ernesto-g/PolySynth/PCB/7th_VOICE_PCB/PCB_TO_PRINT.png

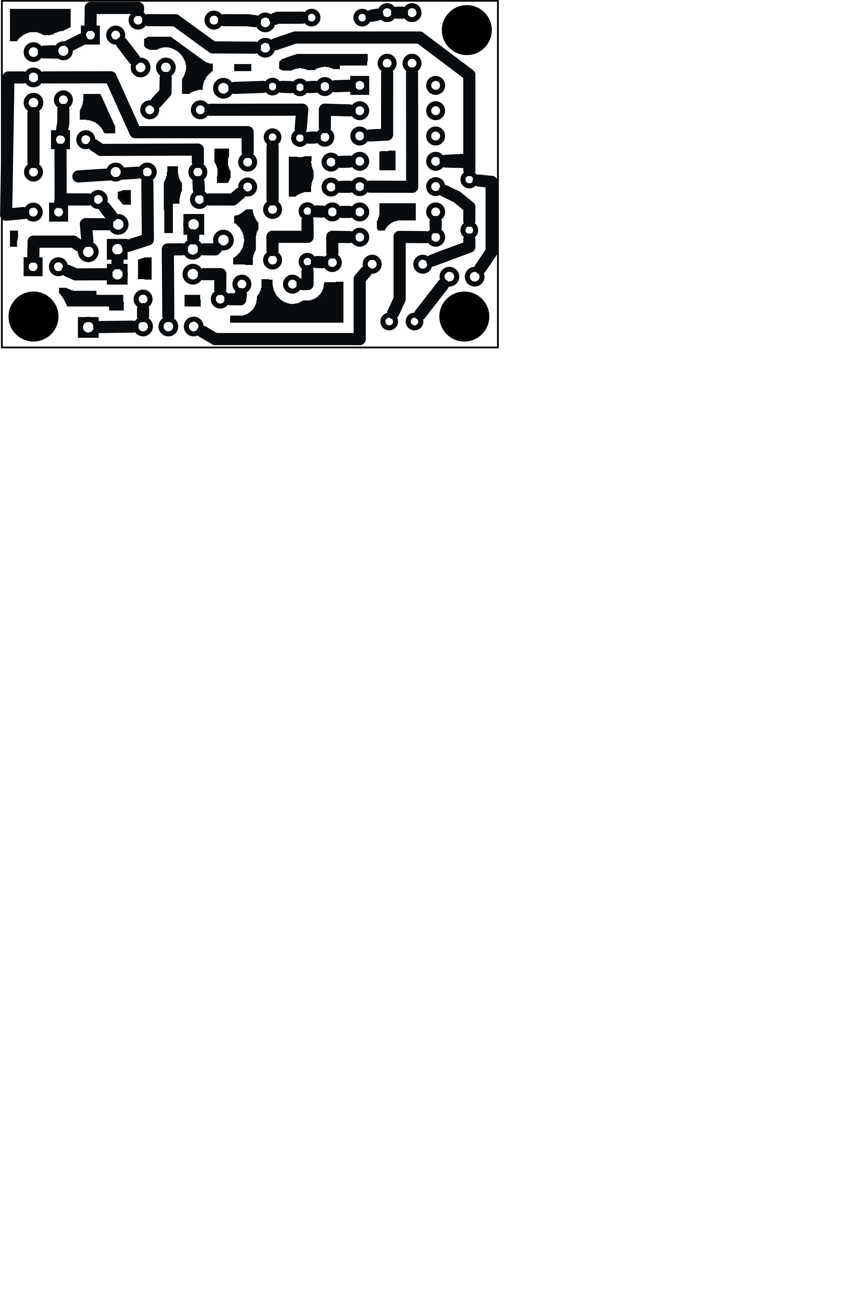
PCB/7th_VOICE_PCB/PCB_TO_PRINT.png
