ernesto-g/PolySynth/PCB/VCF_PCB/VCF_PCB_TO_PRINT.png

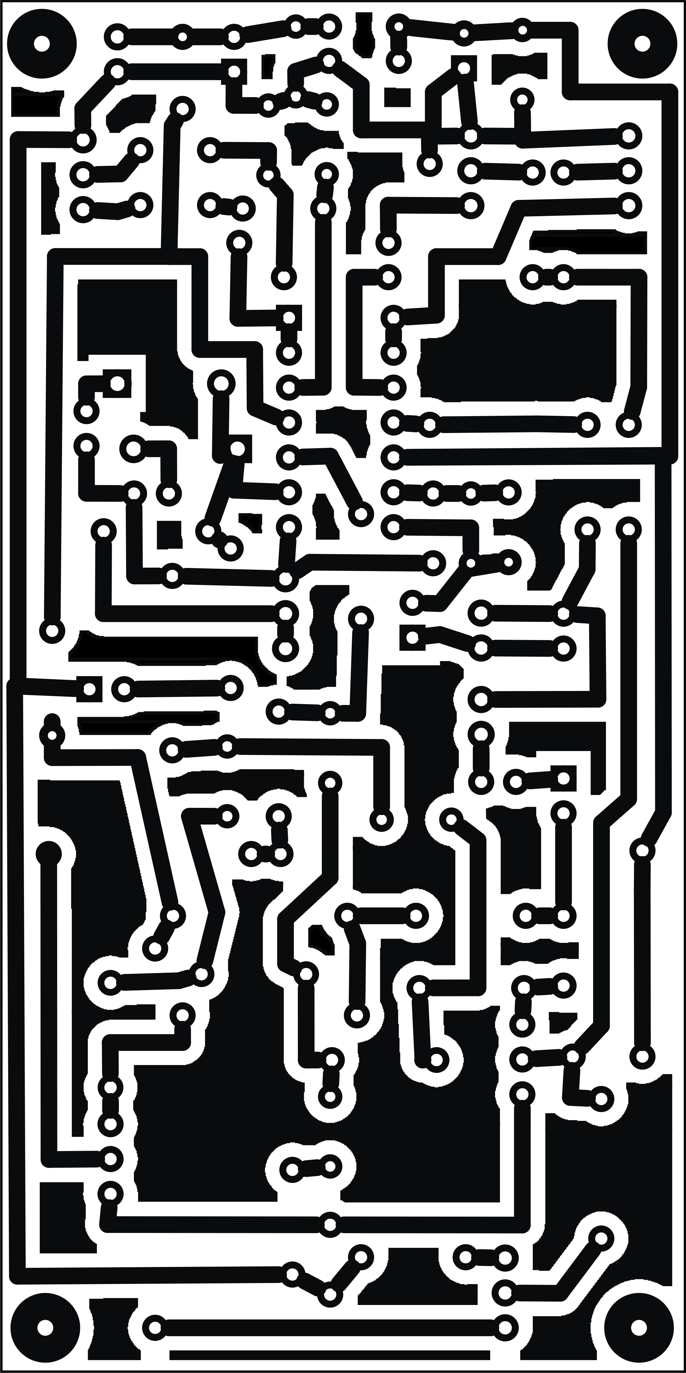
PCB/VCF_PCB/VCF_PCB_TO_PRINT.png
