ernesto-g/PolySynth/PCB/VOICES_PCB/VOICES_PCB_TO_PRINT.png

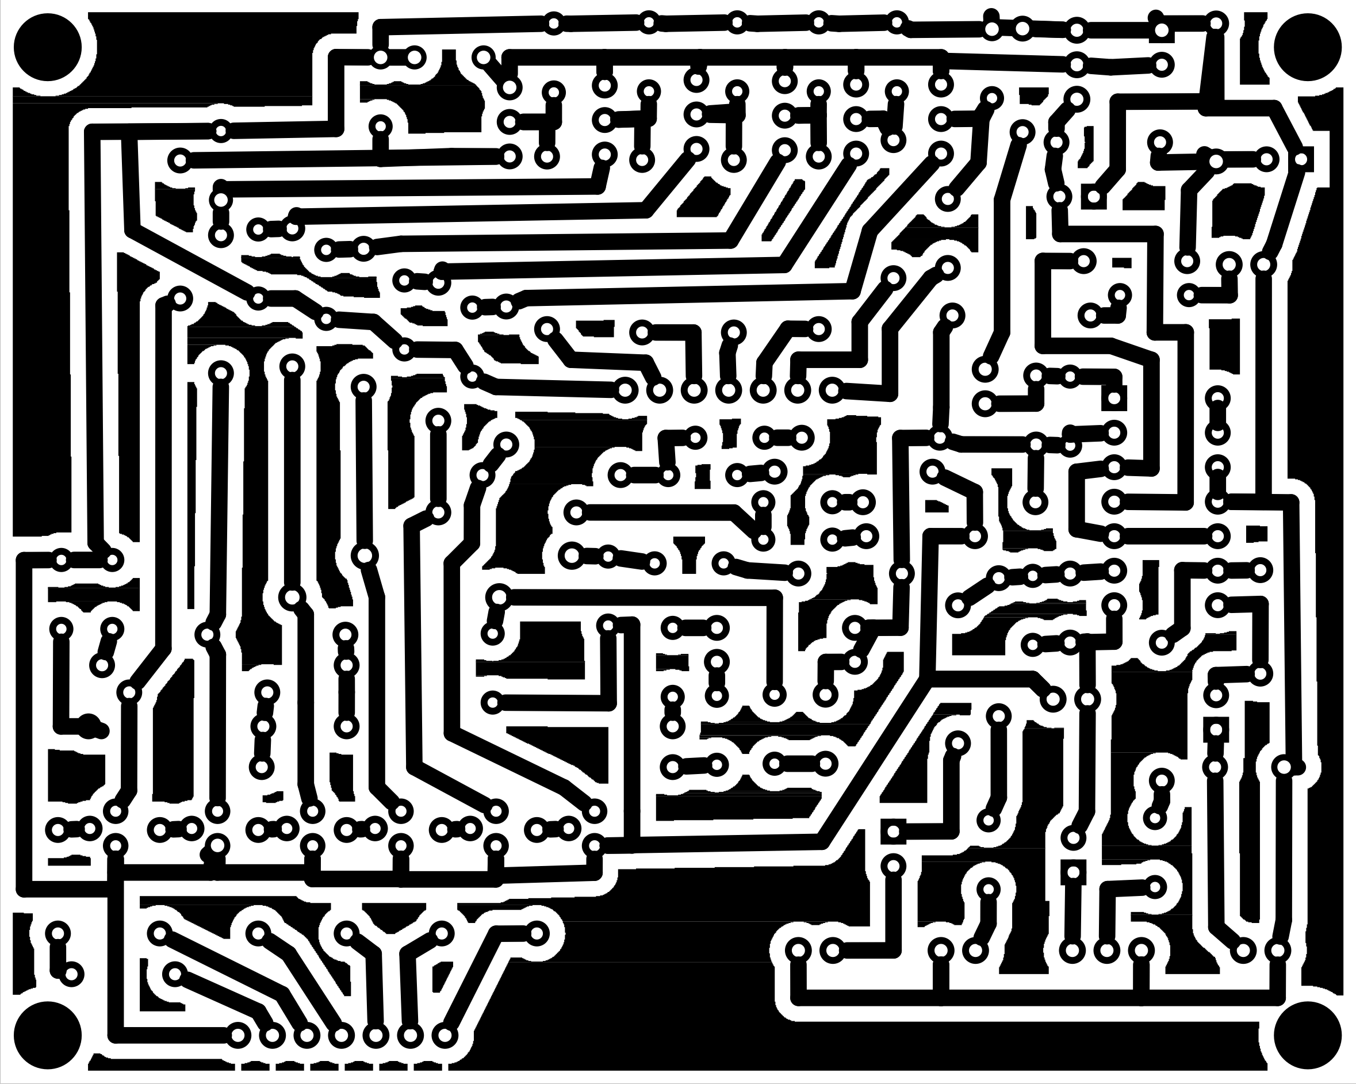
PCB/VOICES_PCB/VOICES_PCB_TO_PRINT.png
