ernesto-g/PolySynth/PCB/DIGITAL_PCB/DIGITAL_etch_silk_bottom.pdf

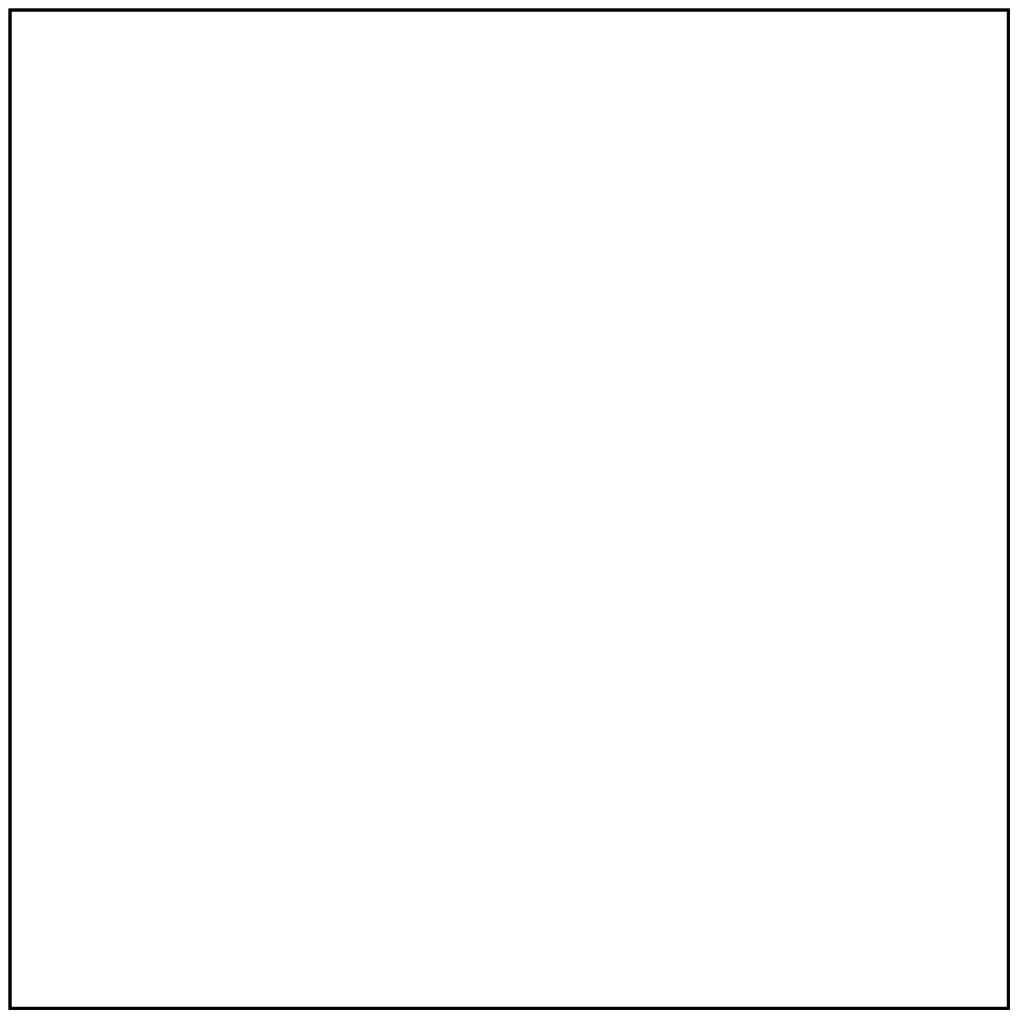
[picture p20: page 1]
