ernesto-g/PolySynth/PCB/DIGITAL_PCB/DIGITAL_etch_silk_top.pdf

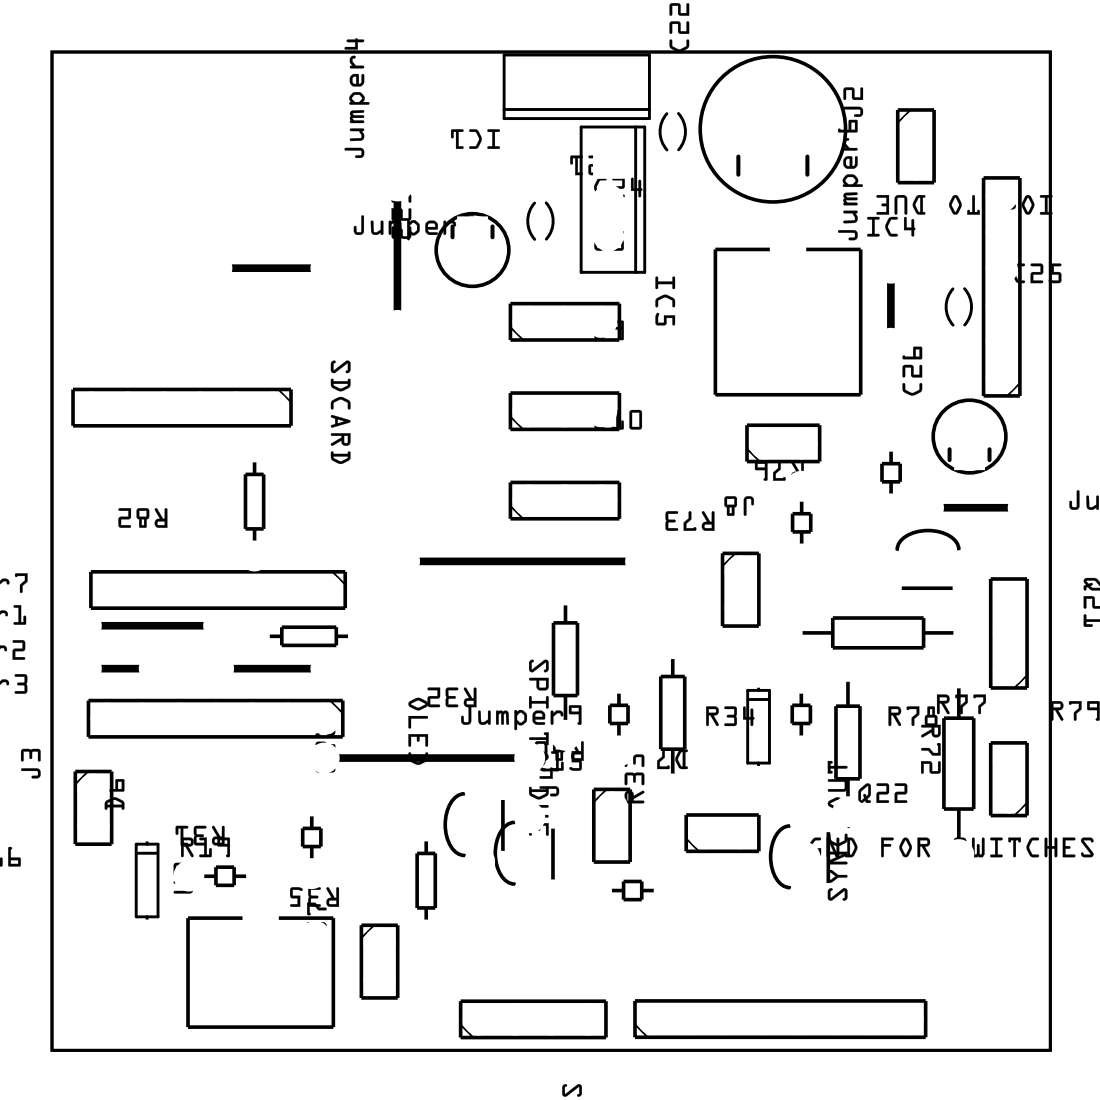
[picture p21: page 1]
