ernesto-g/PolySynth/PCB/DIGITAL_PCB/DIGITAL_etch_silk_top_mirror.pdf

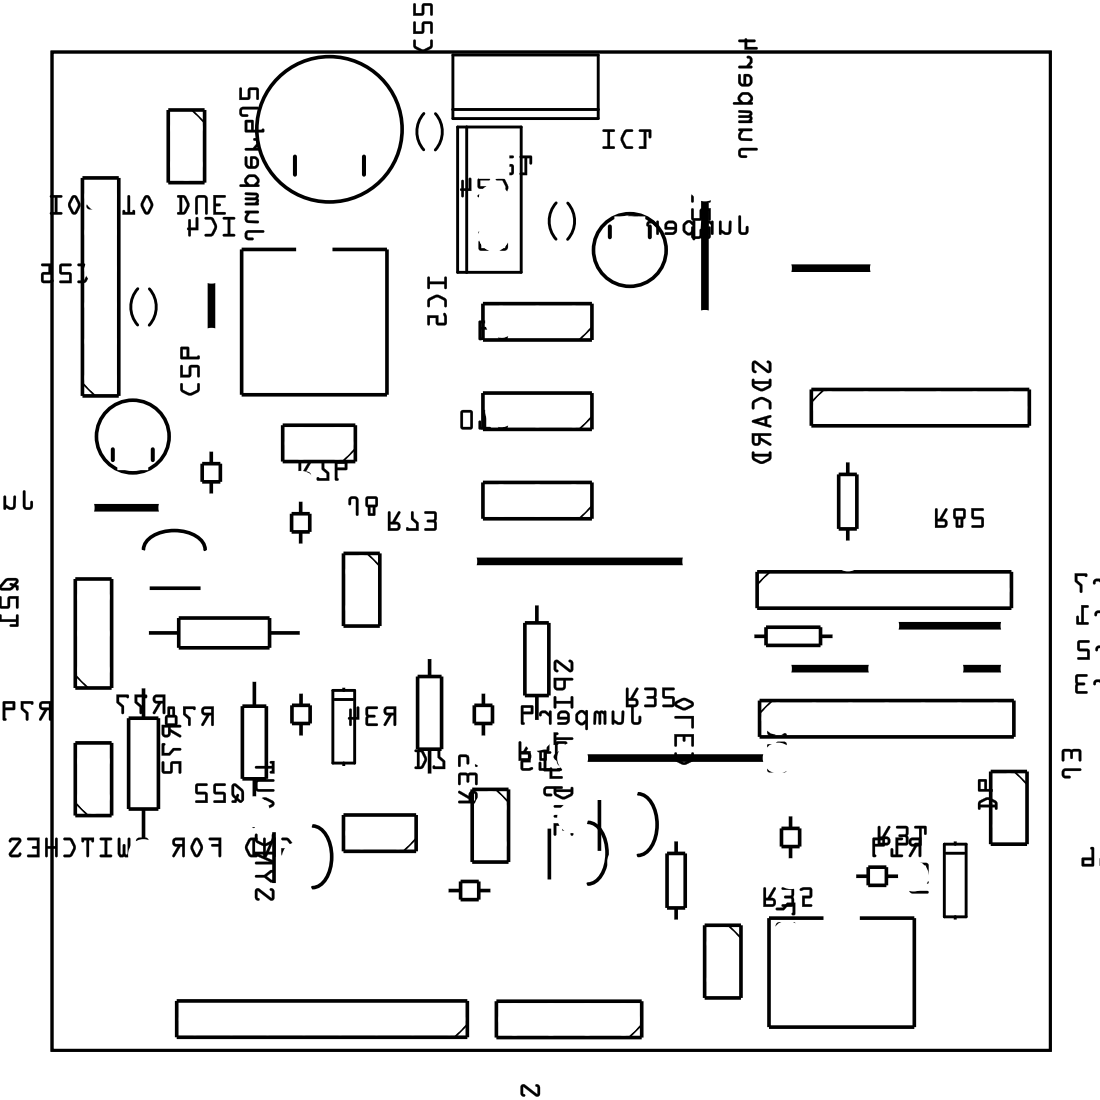
[picture p22: page 1]
