ernesto-g/PolySynth/PCB/VOICES_PCB/VOICES_etch_copper_bottom.pdf

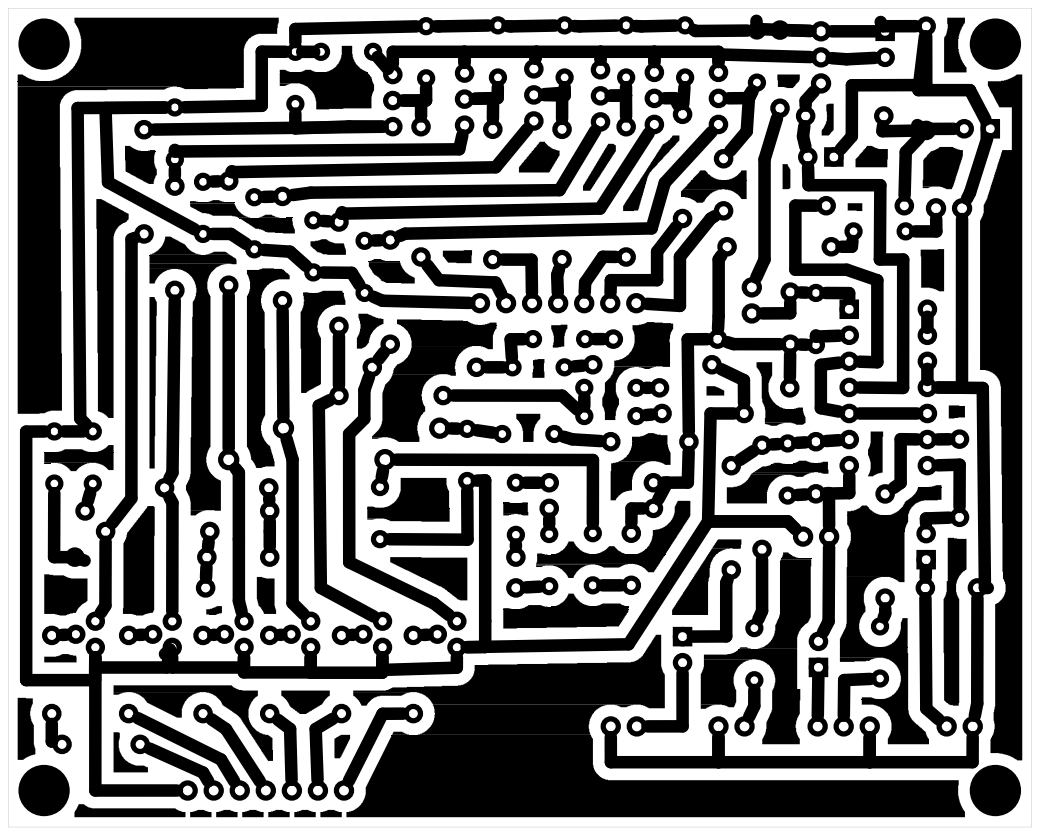
[picture p23: page 1]
