ernesto-g/PolySynth/PCB/VOICES_PCB/VOICES_etch_copper_bottom_mirror.pdf

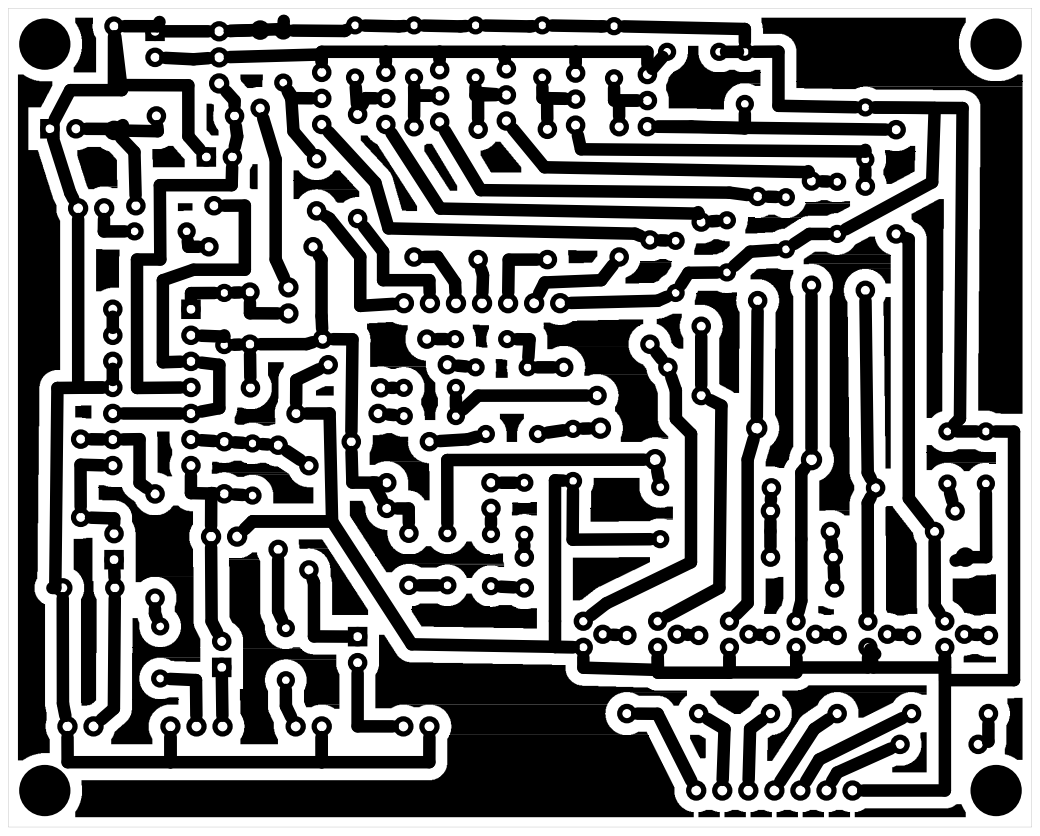
[picture p24: page 1]
