ernesto-g/PolySynth/PCB/VOICES_PCB/VOICES_etch_copper_top.pdf

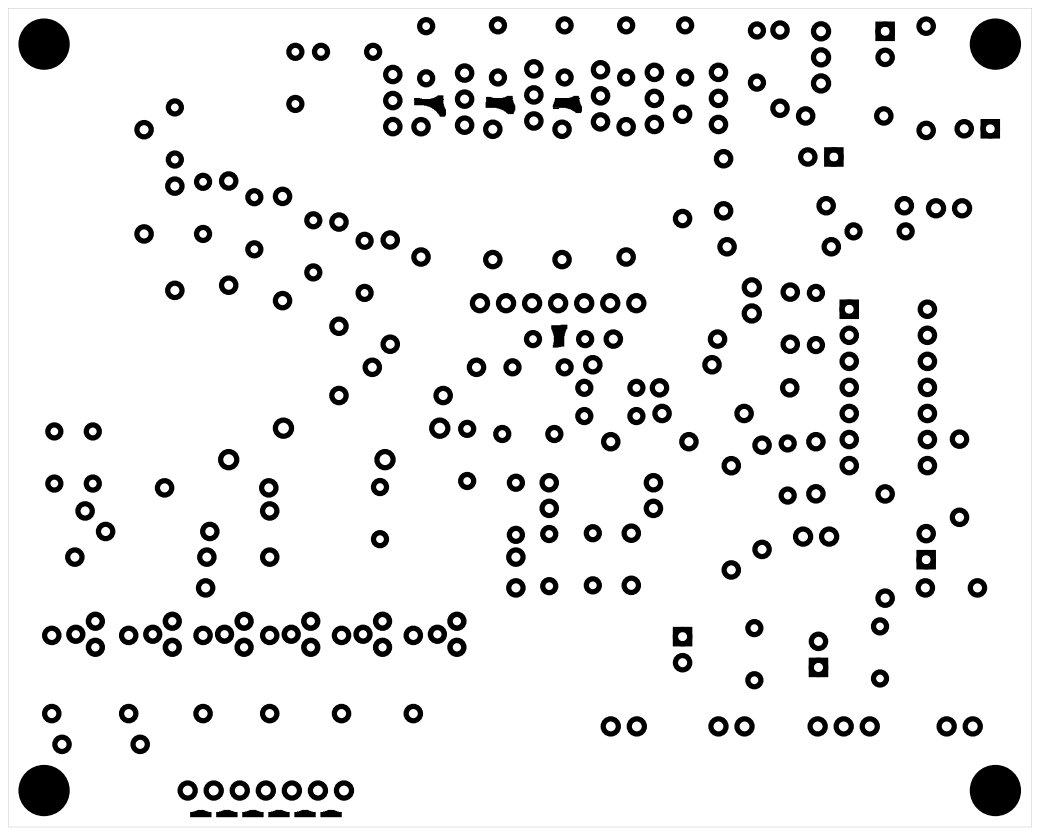
[picture p25: page 1]
