ernesto-g/PolySynth/PCB/VOICES_PCB/VOICES_etch_copper_top_mirror.pdf

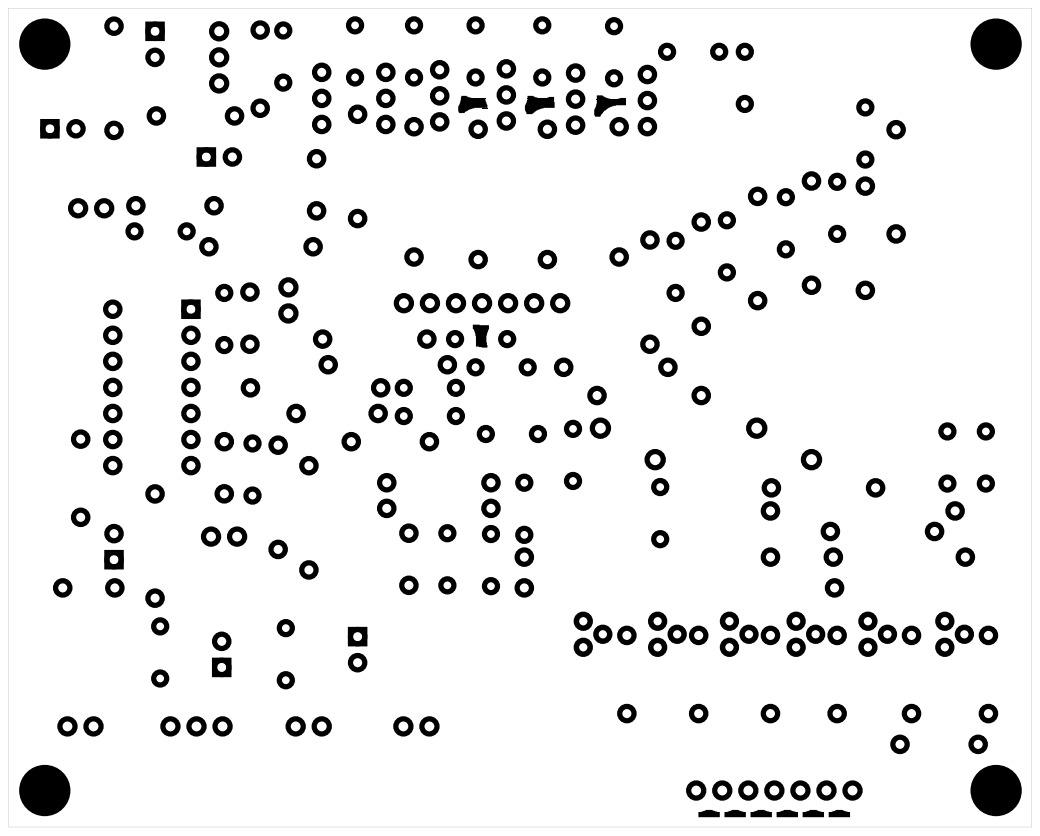
[picture p26: page 1]
