ernesto-g/PolySynth/PCB/VOICES_PCB/VOICES_etch_mask_bottom.pdf

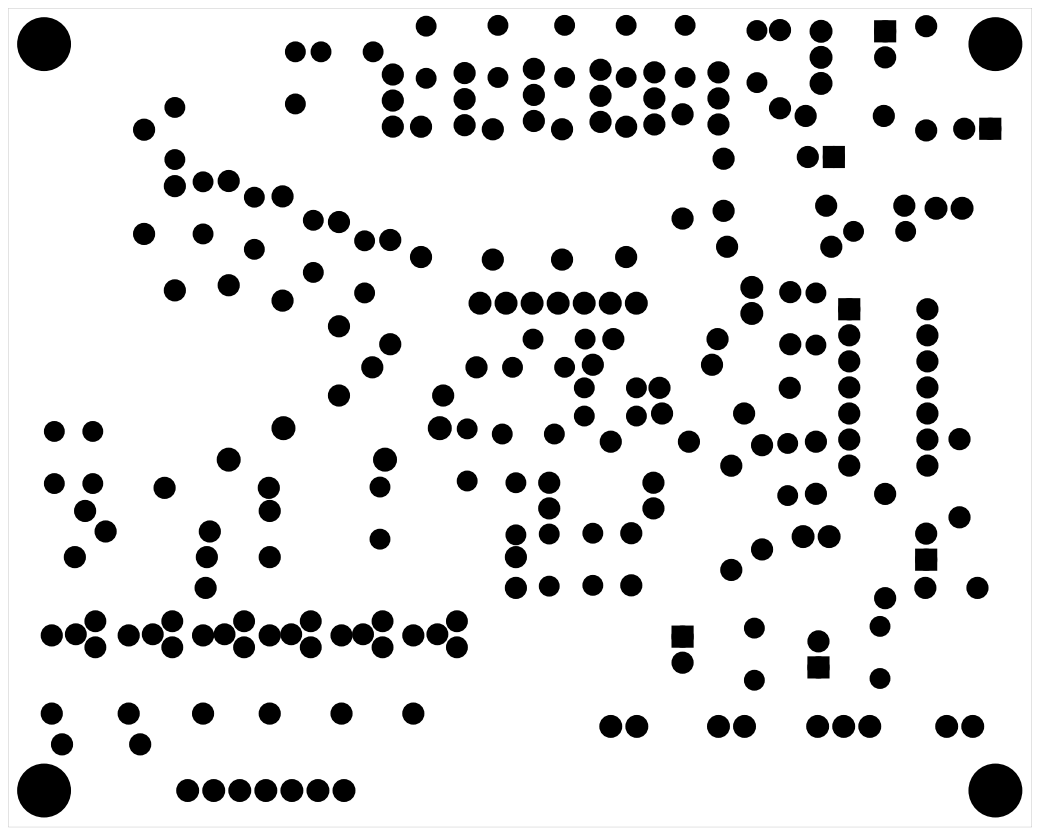
[picture p27: page 1]
