ernesto-g/PolySynth/PCB/VOICES_PCB/VOICES_etch_mask_bottom_mirror.pdf

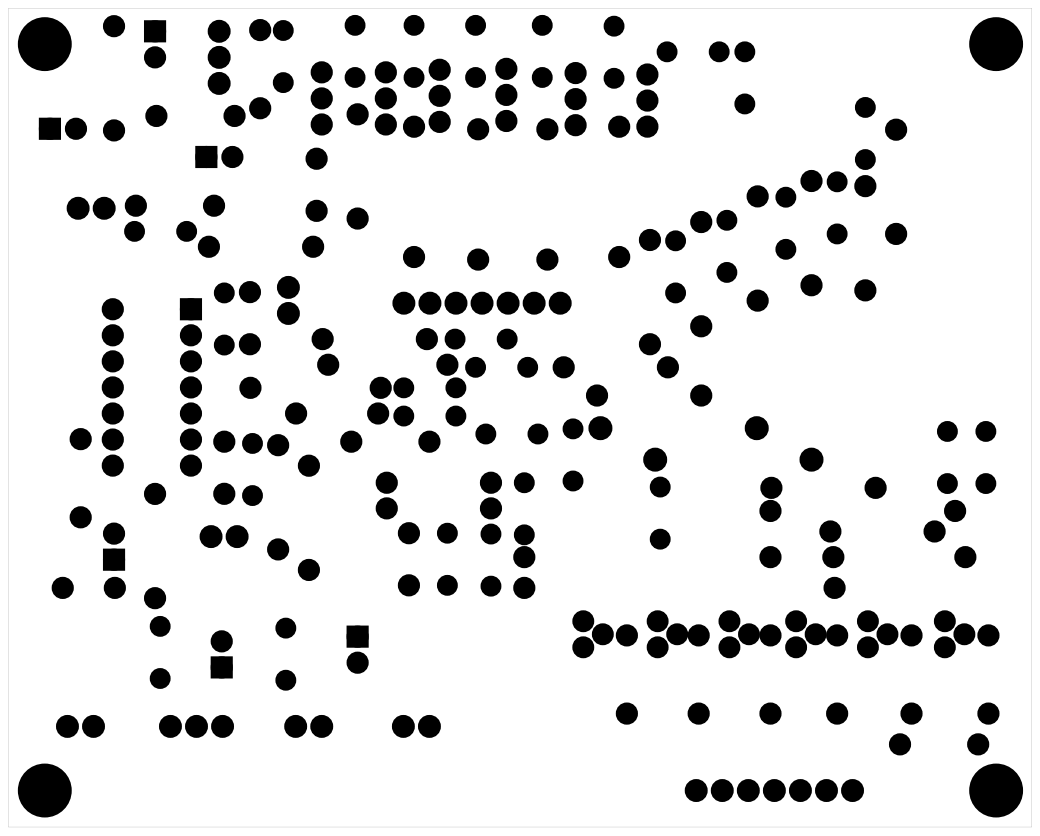
[picture p28: page 1]
