ernesto-g/PolySynth/PCB/VOICES_PCB/VOICES_etch_silk_bottom.pdf

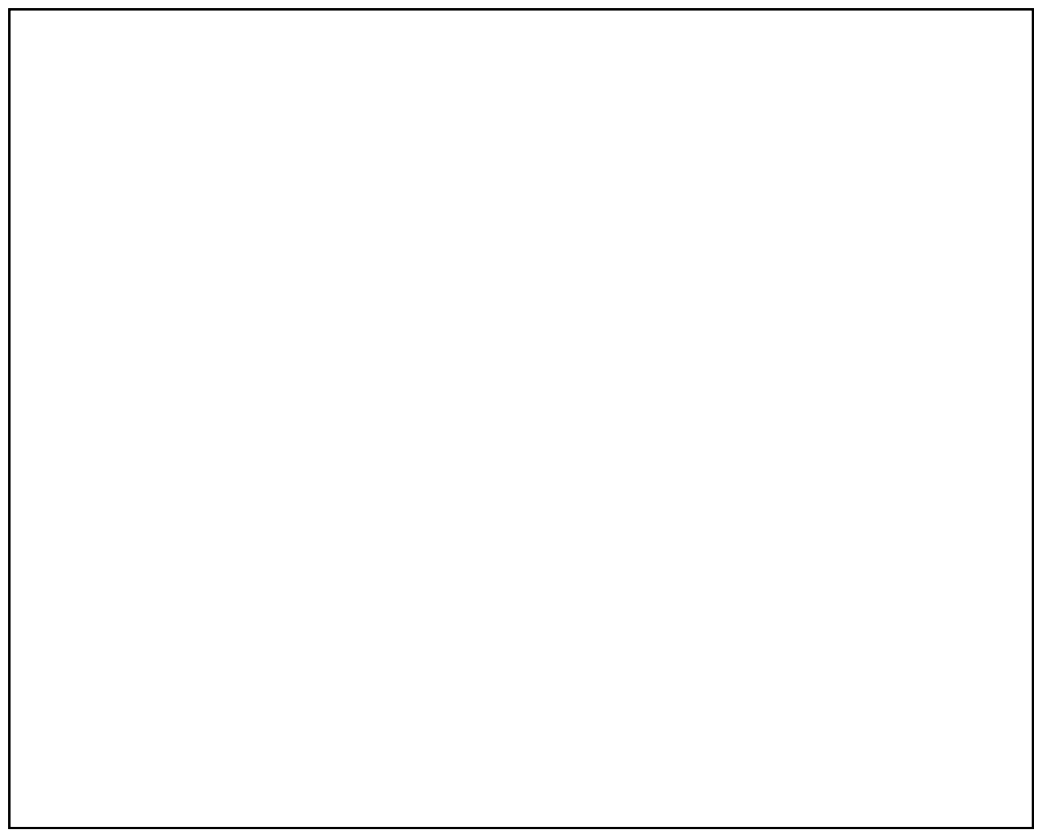
[picture p29: page 1]
