ernesto-g/PolySynth/PCB/VOICES_PCB/VOICES_etch_silk_bottom_mirror.pdf

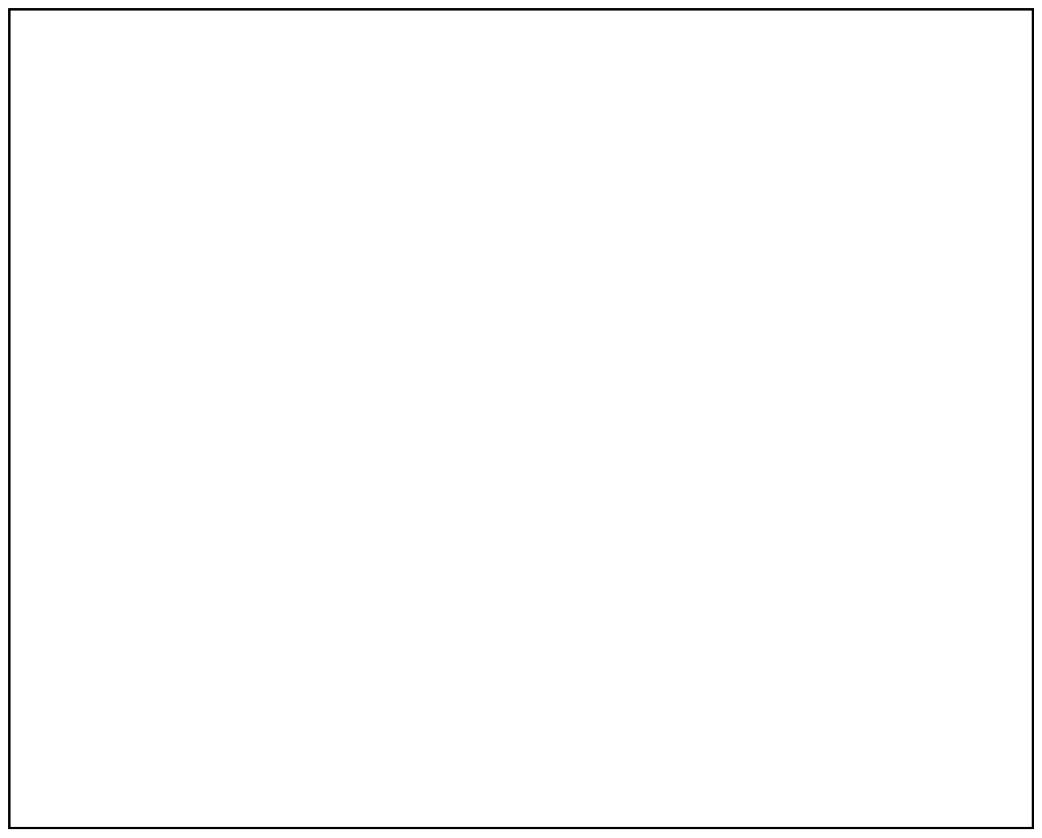
[picture p30: page 1]
