ernesto-g/PolySynth/PCB/VOICES_PCB/VOICES_etch_silk_top.pdf

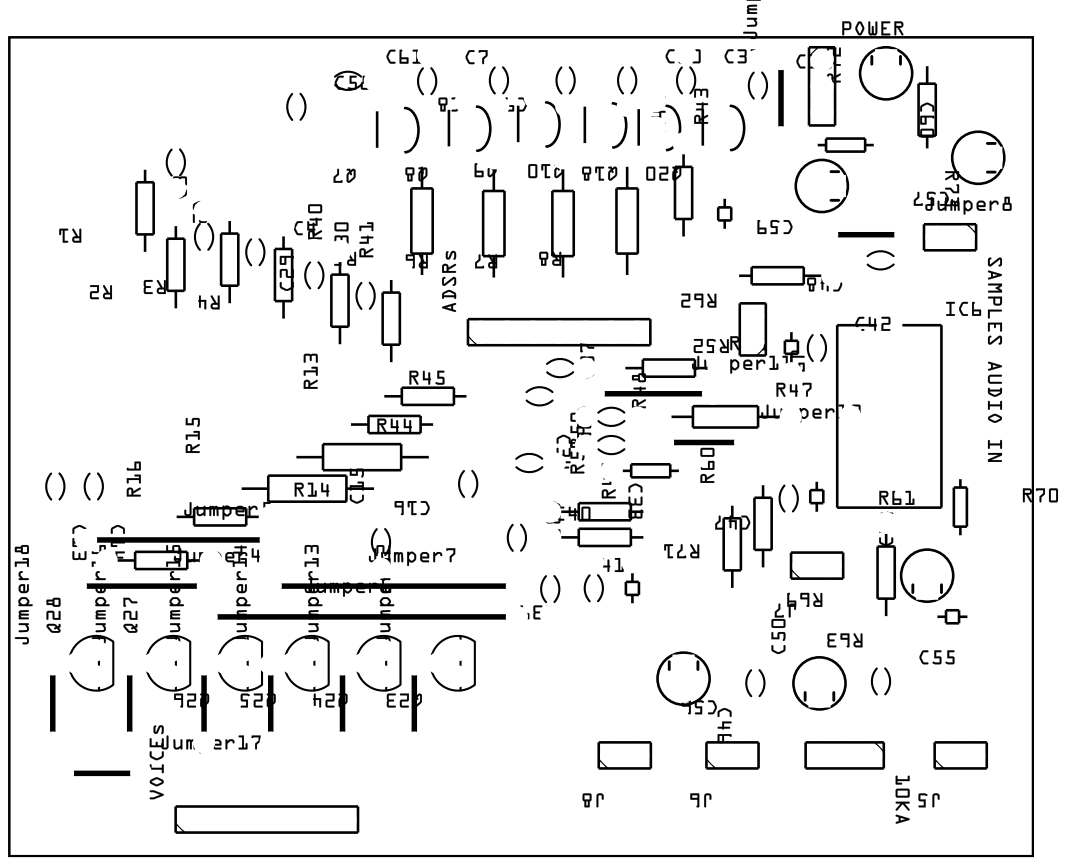
[picture p31: page 1]
