ernesto-g/PolySynth/PCB/VOICES_PCB/VOICES_etch_silk_top_mirror.pdf

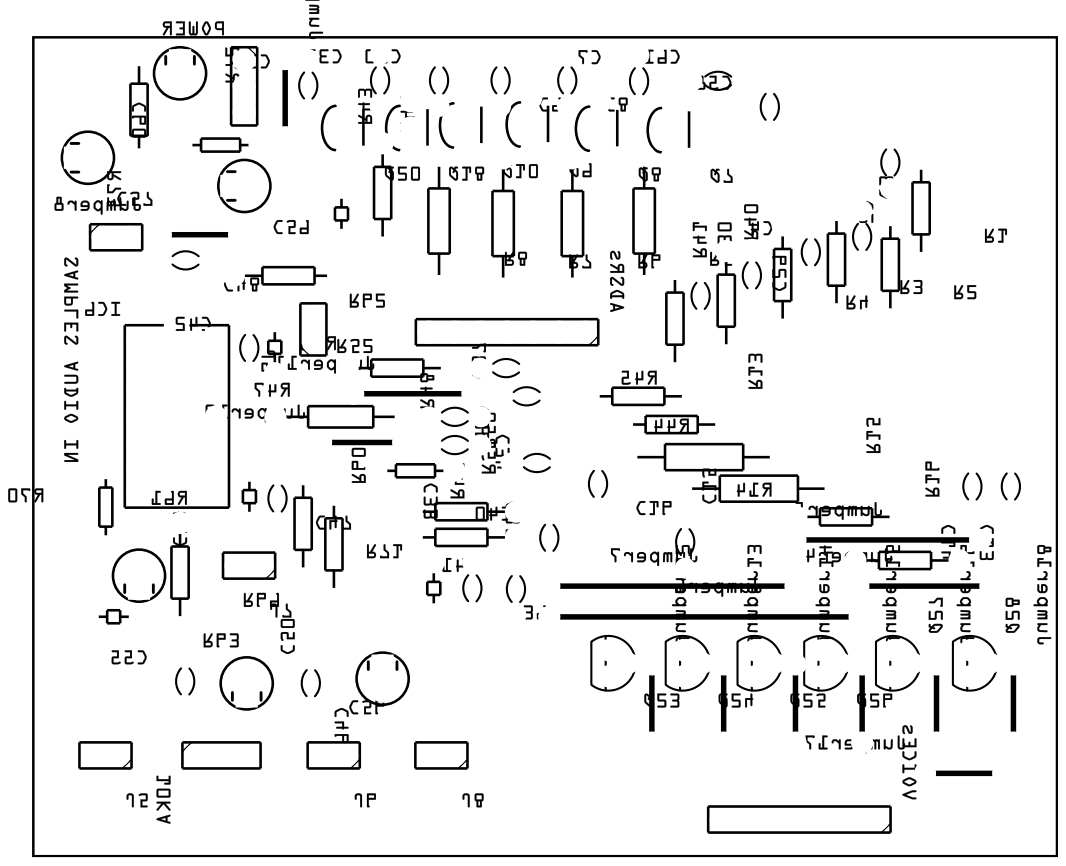
[picture p32: page 1]
