ernesto-g/PolySynth/PCB/VOICES_PCB/VOICES_shematic.pdf

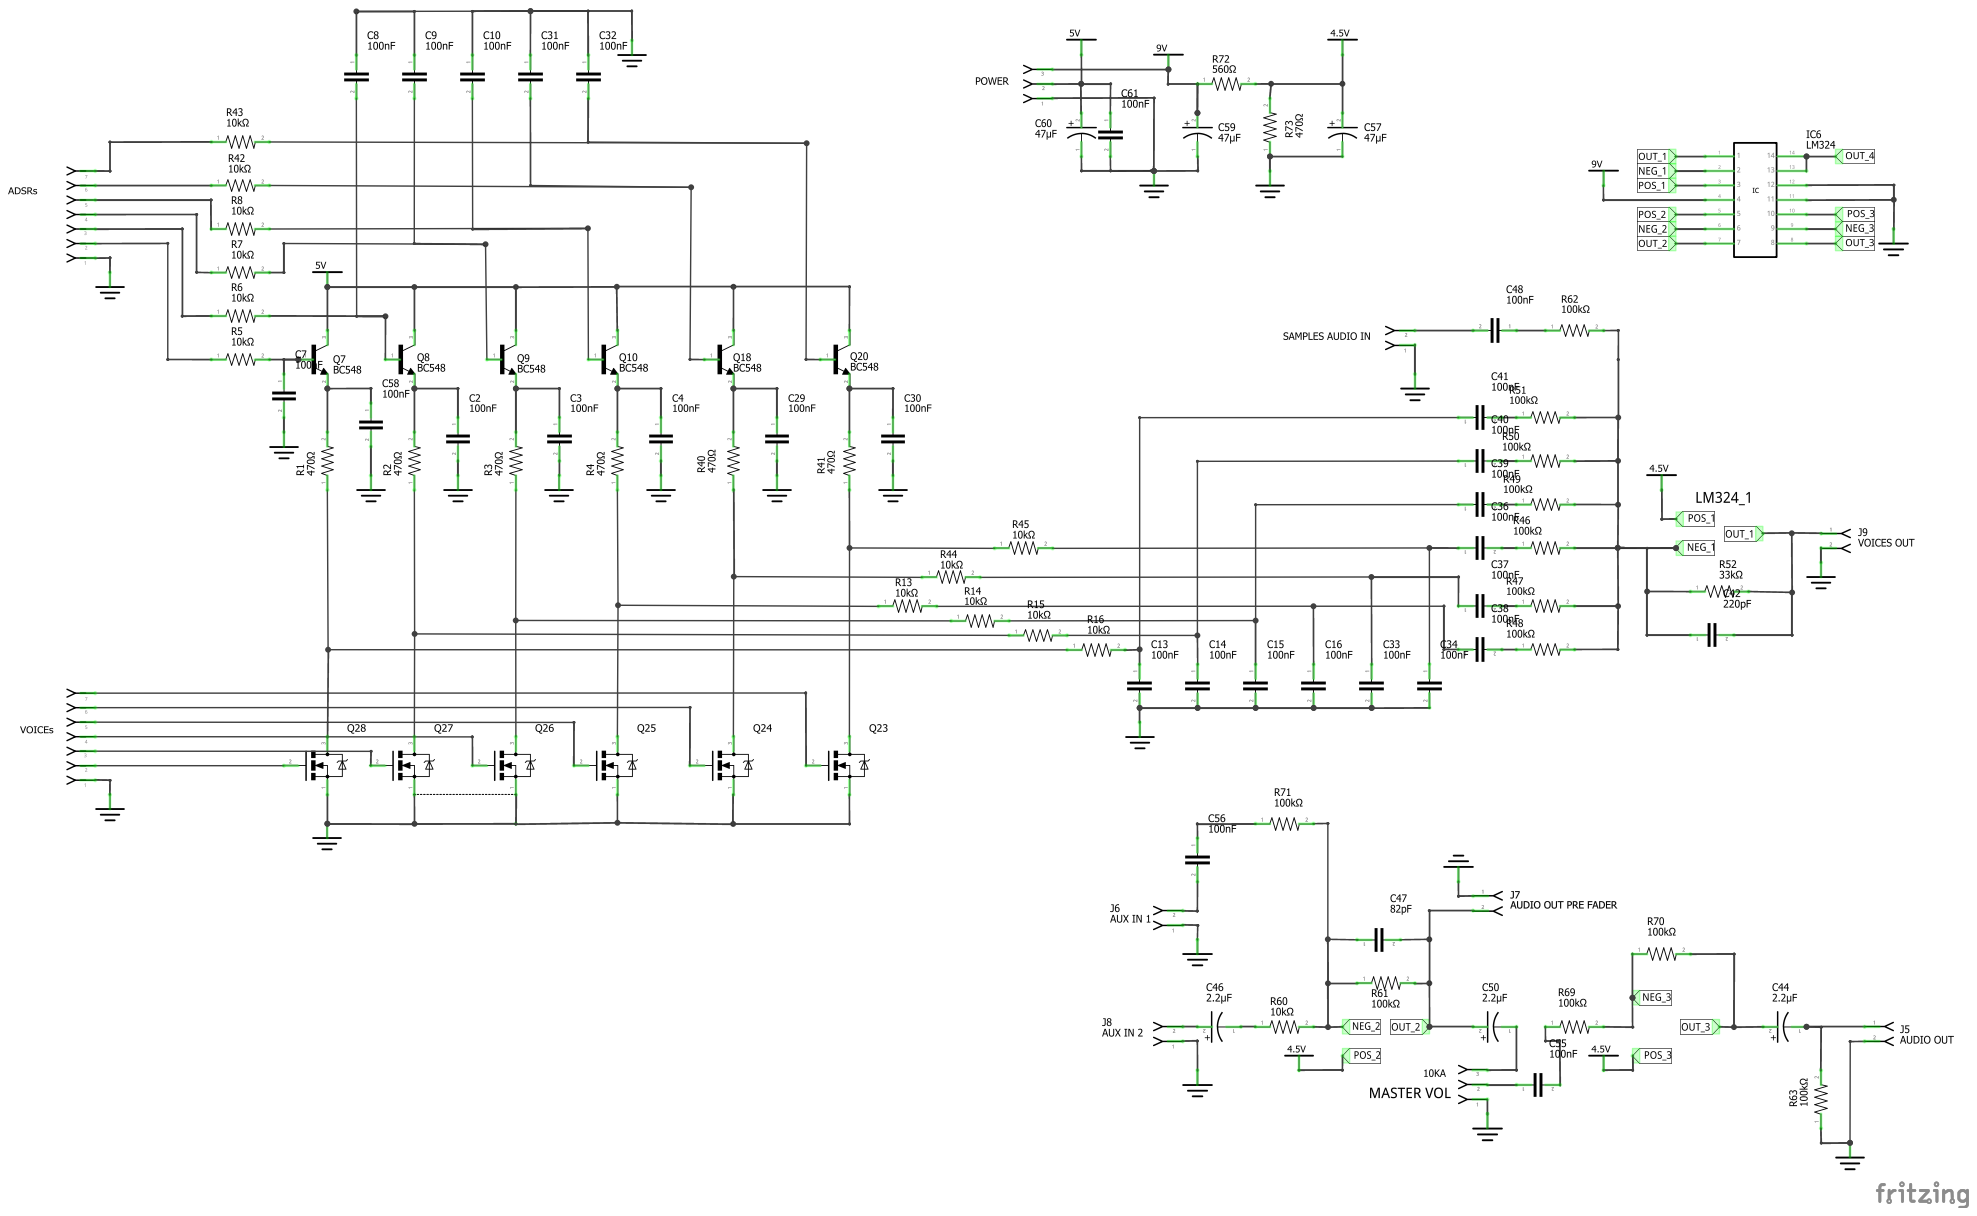
[picture p33: page 1]
