ernesto-g/PolySynth/Main/WaveTables.c

#include <Arduino.h>

#define CASIO_MT600_TABLE_C_LEN 1957
#define CASIO_MT600_TABLE_Cs_LEN 1847
#define CASIO_MT600_TABLE_D_LEN 1743
#define CASIO_MT600_TABLE_Ds_LEN 1646
#define CASIO_MT600_TABLE_E_LEN 1553
#define CASIO_MT600_TABLE_F_LEN 1466
#define CASIO_MT600_TABLE_Fs_LEN 1384
#define CASIO_MT600_TABLE_G_LEN 1306
#define CASIO_MT600_TABLE_Gs_LEN 1233
#define CASIO_MT600_TABLE_A_LEN 1164
#define CASIO_MT600_TABLE_As_LEN 1098
#define CASIO_MT600_TABLE_B_LEN 1037
volatile const unsigned short CASIO_MT600_TABLE_C[CASIO_MT600_TABLE_C_LEN] PROGMEM ={3485,3485,3485,3490,3490,3496,3496,3504,3504,3512,3512,3524,3524,3524,3541,3541,3564,3564,3591,3591,3623,3623,3661,3661,3661,3706,3706,3756,3756,3811,3811,3872,3872,3941,3941,3941,4016,4016,4095,4095,4177,4177,4263,4263,4353,4353,4353,4448,4448,4546,4546,4648,4648,4753,4753,4861,4861,4861,4970,4970,5079,5079,5188,5188,5300,5300,5412,5412,5412,5524,5524,5635,5635,5745,5745,5853,5853,5959,5959,5959,6063,6063,6167,6167,6271,6271,6373,6373,6471,6471,6471,6566,6566,6659,6659,6749,6749,6836,6836,6921,6921,6921,7003,7003,7084,7084,7159,7159,7230,7230,7298,7298,7298,7367,7367,7435,7435,7499,7499,7556,7556,7610,7610,7610,7663,7663,7716,7716,7766,7766,7810,7810,7852,7852,7852,7893,7893,7931,7931,7967,7967,8000,8000,8031,8031,8031,8060,8060,8087,8087,8114,8114,8140,8140,8162,8162,8162,8180,8180,8196,8196,8212,8212,8229,8229,8245,8245,8245,8257,8257,8268,8268,8278,8278,8288,8288,8294,8294,8294,8300,8300,8305,8305,8311,8311,8314,8314,8315,8315,8315,8314,8314,8314,8314,8316,8316,8316,8316,8314,8314,8314,8311,8311,8308,8308,8305,8305,8301,8301,8297,8297,8297,8295,8295,8295,8295,8294,8294,8294,8294,8296,8296,8296,8301,8301,8306,8306,8314,8314,8323,8323,8335,8335,8335,8348,8348,8362,8362,8377,8377,8396,8396,8417,8417,8417,8439,8439,8460,8460,8480,8480,8502,8502,8526,8526,8526,8550,8550,8573,8573,8597,8597,8624,8624,8652,8652,8652,8678,8678,8703,8703,8727,8727,8752,8752,8778,8778,8778,8802,8802,8823,8823,8845,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
2,8422,8446,8446,8470,8470,8493,8493,8493,8517,8517,8541,8541,8568,8568,8594,8594,8619,8619,8619,8643,8643,8667,8667,8691,8691,8715,8715,8737,8737,8737,8759,8759,8781,8781,8803,8803,8824,8824,8845,8845,8845,8866,8866,8886,8886,8904,8904,8920,8920,8934,8934,8934,8949,8949,8963,8963,8977,8977,8989,8989,9001,9001,9001,9012,9012,9022,9022,9033,9033,9041,9041,9050,9050,9050,9058,9058,9064,9064,9069,9069,9073,9073,9076,9076,9076,9081,9081,9085,9085,9088,9088,9090,9090,9091,9091,9091,9093,9093,9093,9093,9091,9091,9088,9088,9085,9085};
volatile const unsigned short CASIO_MT600_TABLE_Cs[CASIO_MT600_TABLE_Cs_LEN] PROGMEM ={3485,3485,3485,3490,3490,3496,3496,3504,3504,3512,3512,3524,3524,3541,3541,3564,3564,3591,3591,3623,3623,3661,3661,3706,3706,3756,3756,3811,3811,3811,3872,3872,3941,3941,4016,4016,4095,4095,4177,4177,4263,4263,4353,4353,4448,4448,4546,4546,4648,4648,4753,4753,4861,4861,4970,4970,4970,5079,5079,5188,5188,5300,5300,5412,5412,5524,5524,5635,5635,5745,5745,5853,5853,5959,5959,6063,6063,6167,6167,6271,6271,6373,6373,6373,6471,6471,6566,6566,6659,6659,6749,6749,6836,6836,6921,6921,7003,7003,7084,7084,7159,7159,7230,7230,7298,7298,7367,7367,7435,7435,7499,7499,7499,7556,7556,7610,7610,7663,7663,7716,7716,7766,7766,7810,7810,7852,7852,7893,7893,7931,7931,7967,7967,8000,8000,8031,8031,8060,8060,8060,8087,8087,8114,8114,8140,8140,8162,8162,8180,8180,8196,8196,8212,8212,8229,8229,8245,8245,8257,8257,8268,8268,8278,8278,8288,8288,8288,8294,8294,8300,8300,8305,8305,8311,8311,8314,8314,8315,8315,8314,8314,8314,8314,8316,8316,8316,8316,8314,8314,8311,8311,8308,8308,8308,8305,8305,8301,8301,8297,8297,8295,8295,8295,8295,8294,8294,8294,8294,8296,8296,8301,8301,8306,8306,8314,8314,8323,8323,8335,8335,8348,8348,8348,8362,8362,8377,8377,8396,8396,8417,8417,8439,8439,8460,8460,8480,8480,8502,8502,8526,8526,8550,8550,8573,8573,8597,8597,8624,8624,8624,8652,8652,8678,8678,8703,8703,8727,8727,8752,8752,8778,8778,8802,8802,8823,8823,8845,8845,8868,8868,8891,8891,8914,8914,8934,8934,8934,8952,8952,8969,8969,8986,898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
};
volatile const unsigned short CASIO_MT600_TABLE_D[CASIO_MT600_TABLE_D_LEN] PROGMEM ={3485,3485,3490,3490,3496,3496,3504,3504,3512,3512,3524,3524,3541,3541,3564,3564,3591,3591,3623,3623,3661,3661,3706,3706,3756,3756,3811,3811,3872,3872,3941,3941,4016,4016,4095,4095,4177,4177,4263,4263,4353,4353,4448,4448,4546,4546,4648,4648,4753,4861,4861,4970,4970,5079,5079,5188,5188,5300,5300,5412,5412,5524,5524,5635,5635,5745,5745,5853,5853,5959,5959,6063,6063,6167,6167,6271,6271,6373,6373,6471,6471,6566,6566,6659,6659,6749,6749,6836,6836,6921,6921,7003,7003,7084,7084,7159,7230,7230,7298,7298,7367,7367,7435,7435,7499,7499,7556,7556,7610,7610,7663,7663,7716,7716,7766,7766,7810,7810,7852,7852,7893,7893,7931,7931,7967,7967,8000,8000,8031,8031,8060,8060,8087,8087,8114,8114,8140,8140,8162,8162,8180,8180,8196,8212,8212,8229,8229,8245,8245,8257,8257,8268,8268,8278,8278,8288,8288,8294,8294,8300,8300,8305,8305,8311,8311,8314,8314,8315,8315,8314,8314,8314,8314,8316,8316,8316,8316,8314,8314,8311,8311,8308,8308,8305,8305,8301,8301,8297,8297,8295,8295,8295,8294,8294,8294,8294,8296,8296,8301,8301,8306,8306,8314,8314,8323,8323,8335,8335,8348,8348,8362,8362,8377,8377,8396,8396,8417,8417,8439,8439,8460,8460,8480,8480,8502,8502,8526,8526,8550,8550,8573,8573,8597,8597,8624,8624,8652,8678,8678,8703,8703,8727,8727,8752,8752,8778,8778,8802,8802,8823,8823,8845,8845,8868,8868,8891,8891,8914,8914,8934,8934,8952,8952,8969,8969,8986,8986,9002,9002,9016,9016,9030,9030,9044,9044,9056,9056,9067,9067,9078,9078,9089,9089,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
88,7923,7956,7956,7986,8015,8015,8042,8068,8068,8090,8110,8110,8128,8128,8146,8163,8163,8177,8190,8190,8201,8211,8211,8220,8229,8229,8237,8237,8243,8247,8247,8249,8251,8251,8253,8255,8255,8256,8255,8255,8253,8253,8250,8248,8248,8246,8242,8242,8238,8234,8234,8233,8234,8234,8236,8236,8237,8238,8238,8240,8246,8246,8256,8268,8268,8281,8294,8294,8307,8307,8322,8340,8340,8359,8379,8379,8400,8422,8422,8446,8470,8470,8493,8493,8517,8541,8541,8568,8594,8594,8619,8643,8643,8667,8691,8691,8715,8715,8737,8759,8759,8781,8803,8803,8824,8845,8845,8866,8886,8886,8904,8904,8920,8934,8934,8949,8963,8963,8977,8989,8989,9001,9012,9012,9022,9022,9033,9041,9041,9050,9058,9058,9064,9069,9069,9073,9076,9076,9081,9081,9085,9088,9088,9090,9091,9091,9093,9093,9093,9091,9088,9088,9085};
volatile const unsigned short CASIO_MT600_TABLE_G[CASIO_MT600_TABLE_G_LEN] PROGMEM ={3485,3485,3490,3496,3496,3504,3512,3512,3524,3541,3541,3564,3591,3591,3623,3661,3661,3706,3756,3756,3811,3872,3872,3941,4016,4095,4095,4177,4263,4263,4353,4448,4448,4546,4648,4648,4753,4861,4861,4970,5079,5079,5188,5300,5300,5412,5524,5635,5635,5745,5853,5853,5959,6063,6063,6167,6271,6271,6373,6471,6471,6566,6659,6659,6749,6836,6836,6921,7003,7084,7084,7159,7230,7230,7298,7367,7367,7435,7499,7499,7556,7610,7610,7663,7716,7716,7766,7810,7810,7852,7893,7931,7931,7967,8000,8000,8031,8060,8060,8087,8114,8114,8140,8162,8162,8180,8196,8196,8212,8229,8229,8245,8257,8268,8268,8278,8288,8288,8294,8300,8300,8305,8311,8311,8314,8315,8315,8314,8314,8314,8316,8316,8316,8314,8311,8311,8308,8305,8301,8301,8297,8295,8295,8295,8294,8294,8294,8296,8296,8301,8306,8306,8314,8323,8323,8335,8348,8348,8362,8377,8396,8396,8417,8439,8439,8460,8480,8480,8502,8526,8526,8550,8573,8573,8597,8624,8624,8652,8678,8678,8703,8727,8752,8752,8778,8802,8802,8823,8845,8845,8868,8891,8891,8914,8934,8934,8952,8969,8969,8986,9002,9002,9016,9030,9044,9044,9056,9067,9067,9078,9089,9089,9100,9108,9108,9114,9118,9118,9124,9131,9131,9138,9144,9144,9147,9149,9150,9150,9149,9149,9149,9149,9151,9151,9152,9149,9149,9145,9140,9140,9137,9134,9134,9131,9127,9127,9122,9116,9109,9109,9102,9095,9095,9090,9085,9085,9078,9069,9069,9060,9050,9050,9039,9028,9028,9017,9006,9006,8995,8981,8981,8965,8946,8921,8921,8890,8851,8851,8804,8751,8751,8688,8614,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
322,8340,8359,8359,8379,8400,8400,8422,8446,8446,8470,8493,8517,8517,8541,8568,8568,8594,8619,8619,8643,8667,8667,8691,8715,8715,8737,8759,8759,8781,8803,8803,8824,8845,8866,8866,8886,8904,8904,8920,8934,8934,8949,8963,8963,8977,8989,8989,9001,9012,9012,9022,9033,9033,9041,9050,9058,9058,9064,9069,9069,9073,9076,9076,9081,9085,9085,9088,9090,9090,9091,9093,9093,9093,9091,9091,9088,9085};
volatile const unsigned short CASIO_MT600_TABLE_Gs[CASIO_MT600_TABLE_Gs_LEN] PROGMEM ={3485,3485,3490,3496,3496,3504,3512,3524,3524,3541,3564,3564,3591,3623,3661,3661,3706,3756,3756,3811,3872,3941,3941,4016,4095,4177,4177,4263,4353,4353,4448,4546,4648,4648,4753,4861,4861,4970,5079,5188,5188,5300,5412,5524,5524,5635,5745,5745,5853,5959,6063,6063,6167,6271,6271,6373,6471,6566,6566,6659,6749,6836,6836,6921,7003,7003,7084,7159,7230,7230,7298,7367,7367,7435,7499,7556,7556,7610,7663,7716,7716,7766,7810,7810,7852,7893,7931,7931,7967,8000,8000,8031,8060,8087,8087,8114,8140,8162,8162,8180,8196,8196,8212,8229,8245,8245,8257,8268,8268,8278,8288,8294,8294,8300,8305,8311,8311,8314,8315,8315,8314,8314,8316,8316,8316,8314,8314,8311,8308,8305,8305,8301,8297,8295,8295,8295,8294,8294,8294,8296,8301,8301,8306,8314,8314,8323,8335,8348,8348,8362,8377,8377,8396,8417,8439,8439,8460,8480,8502,8502,8526,8550,8550,8573,8597,8624,8624,8652,8678,8678,8703,8727,8752,8752,8778,8802,8823,8823,8845,8868,8868,8891,8914,8934,8934,8952,8969,8969,8986,9002,9016,9016,9030,9044,9056,9056,9067,9078,9078,9089,9100,9108,9108,9114,9118,9118,9124,9131,9138,9138,9144,9147,9149,9149,9150,9149,9149,9149,9149,9151,9151,9152,9149,9149,9145,9140,9137,9137,9134,9131,9127,9127,9122,9116,9116,9109,9102,9095,9095,9090,9085,9085,9078,9069,9060,9060,9050,9039,9028,9028,9017,9006,9006,8995,8981,8965,8965,8946,8921,8921,8890,8851,8804,8804,8751,8688,8614,8614,8528,8432,8432,8327,8215,8093,8093,7960,7818,7818,7667,7508,7342,7342,717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
091,9091,9093,9093,9091,9091,9088,9085};
volatile const unsigned short CASIO_MT600_TABLE_A[CASIO_MT600_TABLE_A_LEN] PROGMEM ={3485,3485,3490,3496,3504,3504,3512,3524,3541,3541,3564,3591,3623,3623,3661,3706,3756,3756,3811,3872,3941,4016,4016,4095,4177,4263,4263,4353,4448,4546,4546,4648,4753,4861,4861,4970,5079,5188,5300,5300,5412,5524,5635,5635,5745,5853,5959,5959,6063,6167,6271,6271,6373,6471,6566,6659,6659,6749,6836,6921,6921,7003,7084,7159,7159,7230,7298,7367,7367,7435,7499,7556,7610,7610,7663,7716,7766,7766,7810,7852,7893,7893,7931,7967,8000,8000,8031,8060,8087,8114,8114,8140,8162,8180,8180,8196,8212,8229,8229,8245,8257,8268,8268,8278,8288,8294,8300,8300,8305,8311,8314,8314,8315,8314,8314,8314,8316,8316,8314,8314,8311,8308,8305,8301,8301,8297,8295,8295,8295,8294,8294,8296,8296,8301,8306,8314,8314,8323,8335,8348,8362,8362,8377,8396,8417,8417,8439,8460,8480,8480,8502,8526,8550,8550,8573,8597,8624,8652,8652,8678,8703,8727,8727,8752,8778,8802,8802,8823,8845,8868,8868,8891,8914,8934,8952,8952,8969,8986,9002,9002,9016,9030,9044,9044,9056,9067,9078,9078,9089,9100,9108,9114,9114,9118,9124,9131,9131,9138,9144,9147,9147,9149,9150,9149,9149,9149,9149,9151,9152,9152,9149,9145,9140,9140,9137,9134,9131,9131,9127,9122,9116,9116,9109,9102,9095,9090,9090,9085,9078,9069,9069,9060,9050,9039,9039,9028,9017,9006,9006,8995,8981,8965,8946,8946,8921,8890,8851,8851,8804,8751,8688,8688,8614,8528,8432,8432,8327,8215,8093,7960,7960,7818,7667,7508,7508,7342,7170,6995,6995,6813,6626,6434,6434,6241,6048,5853,5655,5655,5456,5259,5065,5065,4871,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
