ernesto-g/PolySynth/Main/PwmManager.h

#define PWM_FAST_0  0
#define PWM_FAST_1  1
#define PWM_FAST_2  2
#define PWM_FAST_3  3
#define PWM_FAST_4  4
#define PWM_FAST_5  5
#define PWM_FAST_6  6
#define PWM_FAST_7  7

#define PWM_SLOW_0  0
#define PWM_SLOW_1  1
#define PWM_SLOW_2  2
#define PWM_SLOW_3  3
#define PWM_SLOW_4  4
#define PWM_SLOW_5  5
#define PWM_SLOW_6  6
#define PWM_SLOW_7  7

#define PWM_MAX_VALUE 572




// Prototypes
void pwmm_init(void);



void pwmm_setValuePwmSlow(unsigned char index,unsigned int value);
